SolderedElectronics/Alcohol--Ethanol-sensor-MQ3-breakout-with-easyC-hardware-design/OUTPUTS/V1.1.1/Alcohol, Ethanol sensor MQ3 breakout with easyC Pinout.jpg

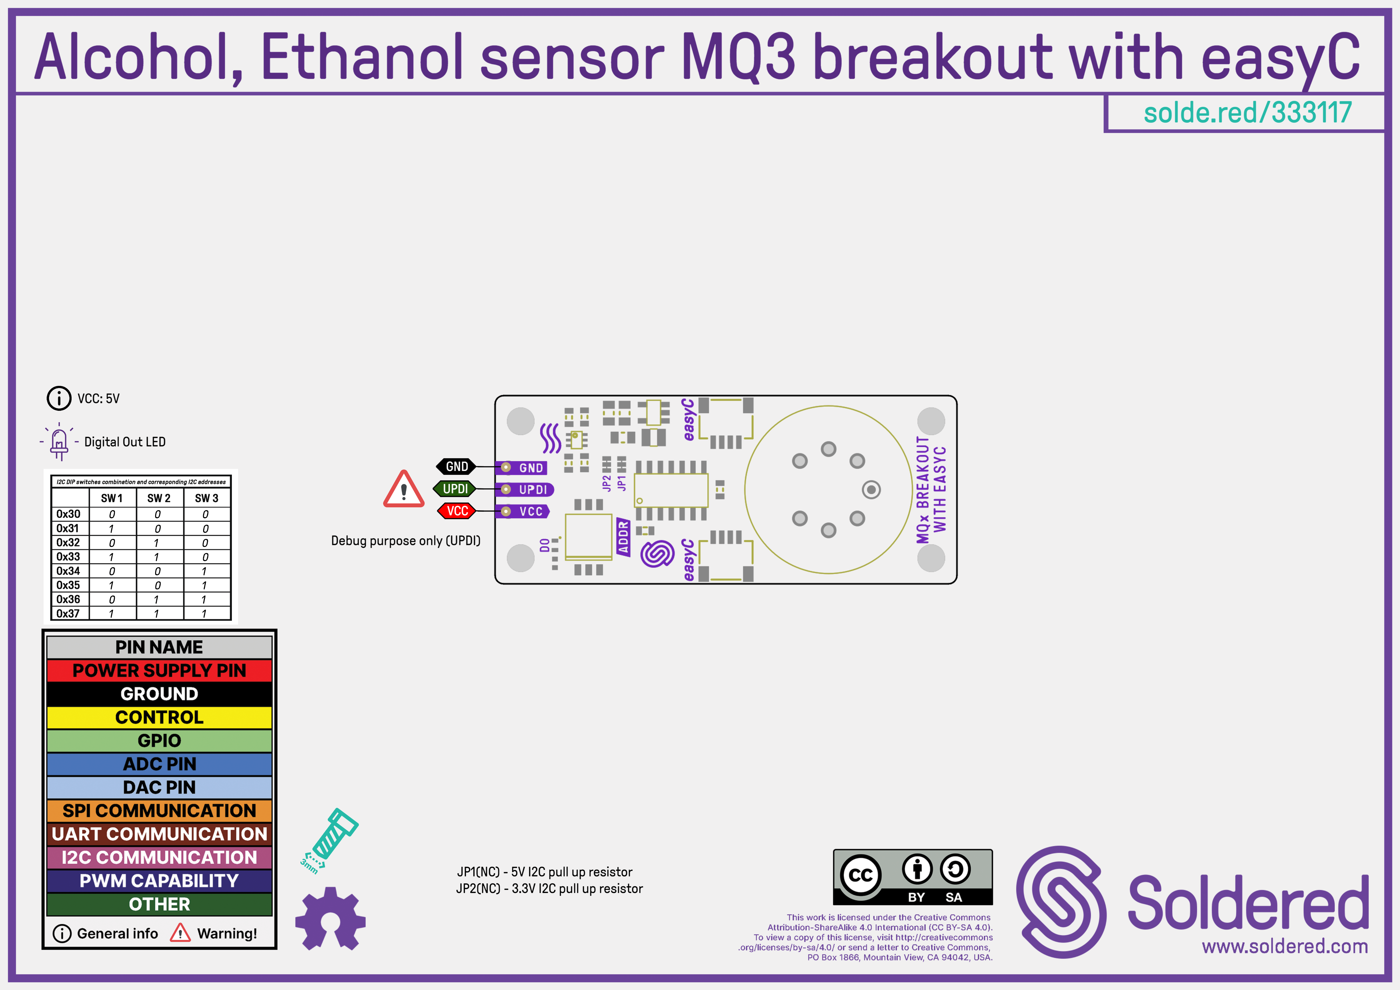
OUTPUTS/V1.1.1/Alcohol, Ethanol sensor MQ3 breakout with easyC Pinout.jpg
